TheFlamethrowerProject/flamethrower/Media/samtax.png

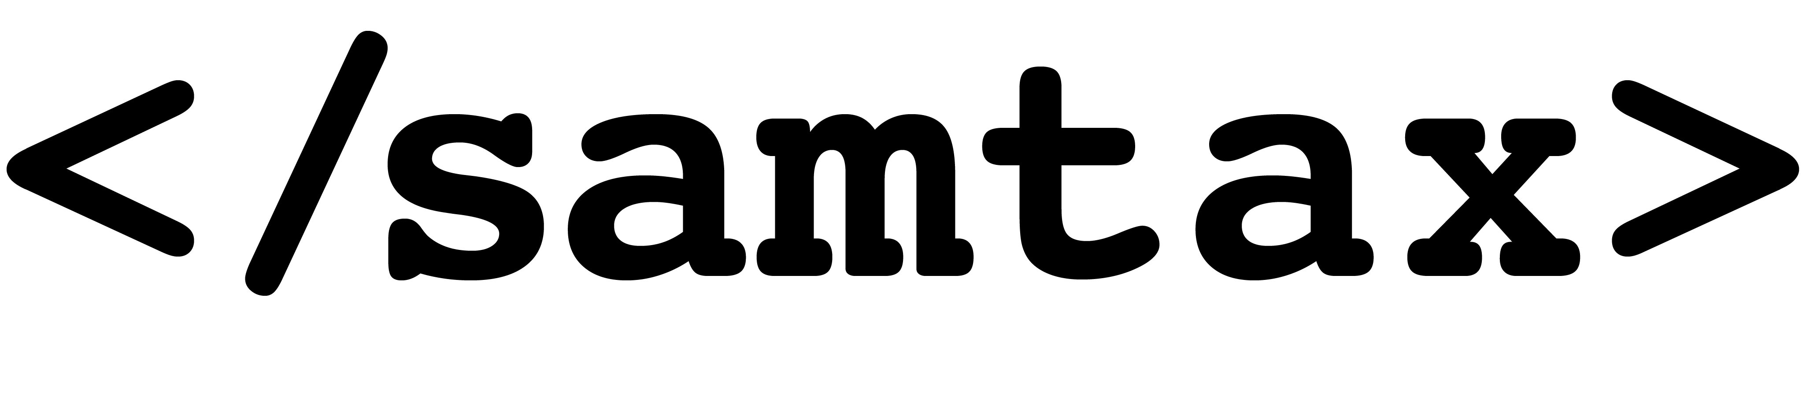
Media/samtax.png
